kerby2000/NorthPoleCircuit/PCB/Pictures/IMG_1404.jpg

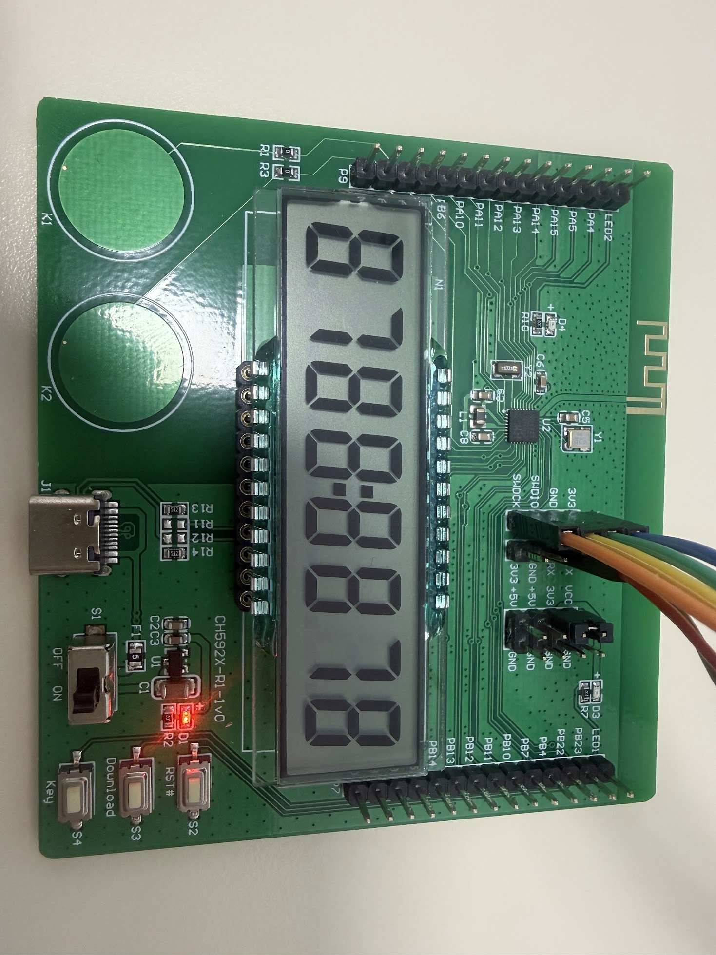
PCB/Pictures/IMG_1404.jpg
