kerby2000/NorthPoleCircuit/PCB/Pictures/IMG_1406.jpg

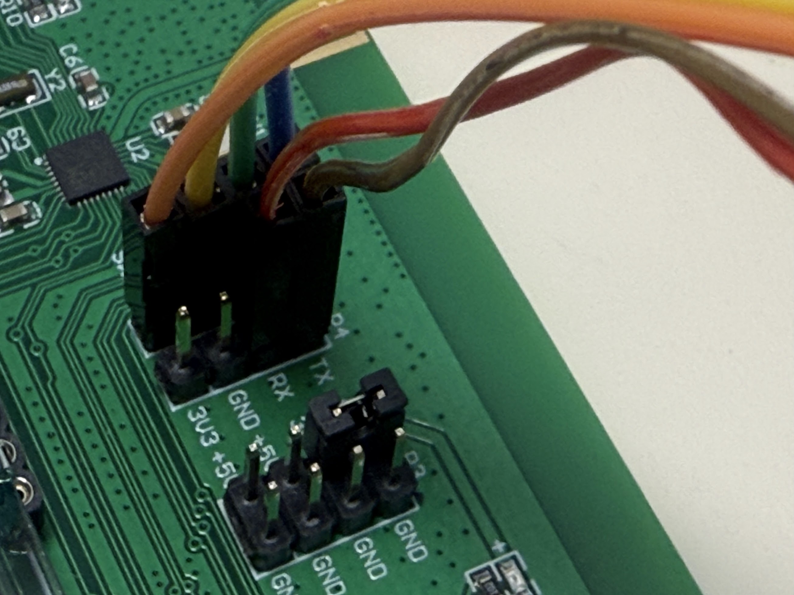
PCB/Pictures/IMG_1406.jpg
