kerby2000/NorthPoleCircuit/PCB/Pictures/IMG_1407.jpg

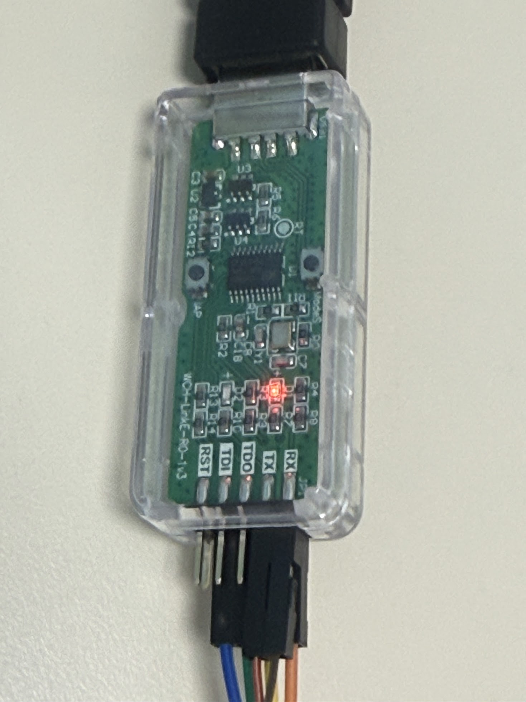
PCB/Pictures/IMG_1407.jpg
