kerby2000/NorthPoleCircuit/PCB/Pictures/IMG_1408.jpg

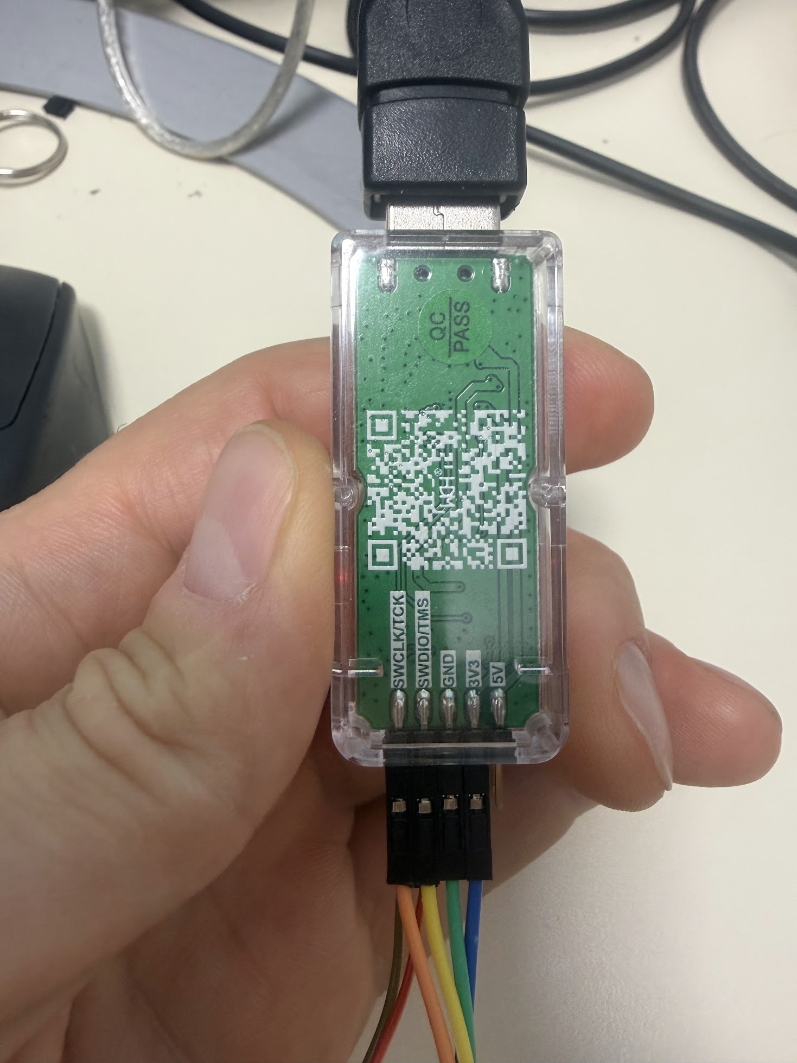
PCB/Pictures/IMG_1408.jpg
