kerby2000/NorthPoleCircuit/Firmware/docs/upload_logs/official_wchisp_tool_result.md

# Official WCH USB ISP Tool Result

Status: PASS, GUI path only

Purpose:

Test the same known-good MounRiver LED probe HEX with the official WCH USB ISP tool.

Input:

```text
Firmware/mounriver_ch592_led_probe/obj/mounriver_ch592_led_probe.hex
```

Record:

- Official tool name/version: WCHISPStudio V3.9, internal `WCHISPTool_CH57x-59x` V3.10.
- Driver binding for `4348:55E0`: official WCH CH375/WCHLink driver stack, not WinUSB/libusb.
- Chip series/model: CH59x / CH592.
- Download port: USB.
- Download config pin: PB22.
- Target file: HEX generated by the probe build, including `Firmware/platformio_ch592_probe/.pio/build/ch592x_wlink_download_mode/firmware.hex` and the known-good MounRiver LED probe HEX candidates.
- Erase/program/verify: PASS.
- Application runs after reset: PASS for LED/LCD-segment probe behavior.

Observed WCHISPStudio V3.9 log:

```text
Device#0 UID:44-46-8F-88-19-70-EC-3E, BTVER:02.30
Begin to download...
BTVER:02.30
Erasing...
Erasing Len: 8K
complete
Programing...
complete
Verifying...
complete
Succeed!
time used:0.358s
```

Interpretation:

```text
Official WCHISPStudio proves that the CH592 native USB Download path, PB22 Download sequence,
USB cable, target power, and HEX image are valid.

The failure of ch32-rs/wchisp is not evidence that native USB ISP is electrically broken.
It is a tool/driver binding problem on Windows.
```

## Protection/Unprotect Finding

WCHISPStudio V3.9 can still flash a CH592 through native USB Download mode after the chip is put in
a protected state, but the tested GUI did not provide an obvious way to unprotect/restore WCH-LinkE
debug attach.

Observed protected-state symptoms:

```text
WCH-LinkUtility / MounRiver:
chip type is not matched or status of chip is wrong

wlink:
Probe is not attached to an MCU, or debug is not enabled
```

Working recovery:

```powershell
# Put CH592 into Download mode.
# Temporarily bind 4348:55E0 / USB Module to WinUSB with Zadig.
$wchisp = "$env:USERPROFILE\.platformio\packages\tool-wchisp\wchisp.exe"
& $wchisp config unprotect
```

After this command, WCH-LinkUtility and MounRiver identified the chip again.

Bring-up rule: keep `Code and data protection mode` unchecked in WCHISPStudio unless intentionally
locking a final production device.

## Command-Line Gap

WCH's WCHISPTool_CMD package was downloaded and inspected.

Observed package contents:

```text
Linux: binaries, source, ISP library/header files
macOS: binary archive and library
Windows: README.md only
```

The Windows README points to the WCHISPTool setup download page. Installing WCHISPTool_Setup.exe
provided WCHISPStudio GUI tools, but no `WCHISPTool_CMD.exe` was found in the tested installation.

Until a Windows WCH-driver-based command-line executable is found or built, the production-safe USB
ISP path is GUI-only.
