kerby2000/NorthPoleCircuit/Firmware/northpole_ch592_bringup/APP/include/board_pins.h

#ifndef BOARD_PINS_H
#define BOARD_PINS_H

#include "board.h"
#include "board_pins_autogen_notes.h"

extern const board_pin_t BOARD_PIN_PWM_A1;
extern const board_pin_t BOARD_PIN_PWM_A2;
extern const board_pin_t BOARD_PIN_PWM_B1;
extern const board_pin_t BOARD_PIN_PWM_B2;
extern const board_pin_t BOARD_PIN_PWM_G1;
extern const board_pin_t BOARD_PIN_PWM_G2;
extern const board_pin_t BOARD_PIN_RGB_DATA;
extern const board_pin_t BOARD_PIN_MOTOR_SLEEP;
extern const board_pin_t BOARD_PIN_AUDIO_BUSY;
extern const board_pin_t BOARD_PIN_HALL1;
extern const board_pin_t BOARD_PIN_HALL2;
extern const board_pin_t BOARD_PIN_TOUCH_SPD_MINUS;
extern const board_pin_t BOARD_PIN_TOUCH_RUN;
extern const board_pin_t BOARD_PIN_TOUCH_SPD_PLUS;
extern const board_pin_t BOARD_PIN_TOUCH_MUSIC;
extern const board_pin_t BOARD_PIN_IP5209_INT;
extern const board_pin_t BOARD_PIN_I2C_SCL;
extern const board_pin_t BOARD_PIN_I2C_SDA;
extern const board_pin_t BOARD_PIN_UART1_TX;
extern const board_pin_t BOARD_PIN_UART1_RX;
extern const board_pin_t BOARD_PIN_USB_DP;
extern const board_pin_t BOARD_PIN_USB_DN;
extern const board_pin_t BOARD_PIN_ANTENNA;

#endif /* BOARD_PINS_H */
