kerby2000/NorthPoleCircuit/Firmware/tools/scope/ip5209_lx_capture.py

#!/usr/bin/env python3
"""Capture IP5209 CSIN/LX waveforms with an OWON/HANMATEK DOS1104 scope."""

from __future__ import annotations

import argparse
import csv
from dataclasses import dataclass, field
from datetime import datetime, timezone
import json
import math
import statistics
import time
from pathlib import Path
import sys
from typing import Any

if __package__ is None or __package__ == "":
    sys.path.insert(0, str(Path(__file__).resolve().parent))

from scope_driver_adapter import ChannelConfig, OwonScopeAdapter, ScopeConnection


REPO_ROOT = Path(__file__).resolve().parents[3]
DEFAULT_EVIDENCE_DIR = REPO_ROOT / "Firmware" / "docs" / "ip5209_scope_evidence"
DEFAULT_REPORT_PATH = REPO_ROOT / "Firmware" / "docs" / "ip5209_lx_scope_report.md"
DEFAULT_FIRMWARE_IMAGE = "Firmware/build/bringup/northpole_ch592_bringup.hex"


@dataclass
class PulseCandidate:
    channel: int
    start_s: float
    end_s: float
    width_s: float
    baseline_v: float
    min_v: float
    max_v: float
    amplitude_v: float
    direction: str
    sample_count: int


@dataclass
class WaveformStats:
    channel: int
    signal: str
    sample_count: int
    min_v: float
    max_v: float
    mean_v: float
    peak_to_peak_v: float
    edge_count: int = 0
    estimated_frequency_hz: float | None = None
    pulse_count: int = 0
    first_pulse_s: float | None = None
    largest_pulse_v: float | None = None
    largest_pulse_width_s: float | None = None


@dataclass
class ScaleCheck:
    channel: int
    signal: str
    dmm_reference_v: float
    raw_mean_v: float
    ratio: float
    status: str


@dataclass
class CaptureResult:
    label: str
    mode: str
    screenshot_path: Path | None = None
    csv_path: Path | None = None
    trigger_status: str | None = None
    classification: str = "PENDING_CAPTURE"
    stats: list[WaveformStats] = field(default_factory=list)
    pulses: dict[int, list[PulseCandidate]] = field(default_factory=dict)
    scale_checks: list[ScaleCheck] = field(default_factory=list)
    scope_settings: dict[str, Any] = field(default_factory=dict)
    warnings: list[str] = field(default_factory=list)
    notes: list[str] = field(default_factory=list)


def build_parser() -> argparse.ArgumentParser:
    parser = argparse.ArgumentParser(description=__doc__)
    parser.add_argument(
        "--mode",
        choices=["idle", "wake-single", "steady-switching", "load-test"],
        help="Capture mode.",
    )
    parser.add_argument("--check-scope", action="store_true", help="Only open the scope and query *IDN?.")
    parser.add_argument(
        "--rewrite-report-only",
        action="store_true",
        help="Reanalyze existing capture CSV files from the manifest and rebuild the report without opening the scope.",
    )
    parser.add_argument("--out-dir", default=str(DEFAULT_EVIDENCE_DIR), help="Evidence output directory.")
    parser.add_argument("--report", default=str(DEFAULT_REPORT_PATH), help="Markdown report path.")
    parser.add_argument(
        "--instrumentkit-src",
        default=str(Path.home() / "Documents" / "VS code projects" / "InstrumentKit" / "src"),
        help="Path to local InstrumentKit src.",
    )
    parser.add_argument("--vid", default="0x5345", help="Scope USB VID.")
    parser.add_argument("--pid", default="0x1234", help="Scope USB PID.")
    parser.add_argument("--timeout-s", type=float, default=2.0, help="Scope USB timeout.")
    parser.add_argument("--probe", type=int, default=1, help="Probe attenuation configured on the scope.")
    parser.add_argument("--ch1-scale", type=float, default=2.0, help="CH1 volts/div.")
    parser.add_argument("--ch2-scale", type=float, default=2.0, help="CH2 volts/div.")
    parser.add_argument("--ch3", choices=["off", "vout"], default="off", help="Optional CH3 signal.")
    parser.add_argument("--ch4", choices=["off", "key", "vreg"], default="off", help="Optional CH4 signal.")
    parser.add_argument("--ch3-scale", type=float, default=2.0, help="CH3 volts/div.")
    parser.add_argument("--ch4-scale", type=float, default=1.0, help="CH4 volts/div.")
    parser.add_argument("--ch1-dmm-v", type=float, default=None, help="Optional DMM reference voltage for CH1.")
    parser.add_argument("--ch2-dmm-v", type=float, default=None, help="Optional DMM reference voltage for CH2.")
    parser.add_argument("--ch3-dmm-v", type=float, default=None, help="Optional DMM reference voltage for CH3.")
    parser.add_argument("--ch4-dmm-v", type=float, default=None, help="Optional DMM reference voltage for CH4.")
    parser.add_argument(
        "--pulse-min-vpp",
        type=float,
        default=0.5,
        help="Minimum peak-to-peak voltage before a channel can be treated as pulsing.",
    )
    parser.add_argument(
        "--pulse-threshold-v",
        type=float,
        default=0.5,
        help="Minimum excursion from baseline for pulse candidate detection.",
    )
    parser.add_argument("--idle-timebase", type=float, default=0.010, help="Idle seconds/div.")
    parser.add_argument("--wake-timebase", type=float, default=0.000100, help="Wake seconds/div.")
    parser.add_argument("--trigger-level", type=float, default=2.0, help="CH2 falling-edge trigger level.")
    parser.add_argument("--wait-trigger-s", type=float, default=10.0, help="Wake trigger wait time.")
    parser.add_argument("--no-waveform", action="store_true", help="Skip waveform CSV reads.")
    parser.add_argument("--no-screenshot", action="store_true", help="Skip screenshot capture.")
    parser.add_argument("--no-prompt", action="store_true", help="Do not wait for user prompts.")
    parser.add_argument("--board-revision", default="north-pole-ble-audio-current-pcb")
    parser.add_argument("--firmware-image", default=DEFAULT_FIRMWARE_IMAGE)
    parser.add_argument("--battery-voltage", default="unknown")
    parser.add_argument("--usb-state", default="unknown", help="connected, disconnected, or unknown.")
    parser.add_argument("--load-ohms", default="220", help="Load value for load-test report text.")
    return parser


def main(argv: list[str] | None = None) -> int:
    parser = build_parser()
    args = parser.parse_args(argv)
    if not args.check_scope and not args.rewrite_report_only and args.mode is None:
        parser.error("--mode is required unless --check-scope is used")

    out_dir = Path(args.out_dir)
    out_dir.mkdir(parents=True, exist_ok=True)

    if args.rewrite_report_only:
        records = load_manifest(out_dir)
        records = reanalyze_records(records, args)
        write_manifest(out_dir, records)
        write_report(Path(args.report), records)
        print(f"report={Path(args.report)}")
        return 0

    connection = ScopeConnection(
        instrumentkit_src=Path(args.instrumentkit_src),
        vid=int(str(args.vid), 0),
        pid=int(str(args.pid), 0),
        timeout_s=args.timeout_s,
    )

    with OwonScopeAdapter(connection) as scope:
        scope_idn = scope.identify()
        if args.check_scope:
            print(f"scope_idn={scope_idn}")
            return 0

        if args.mode == "idle":
            results = [capture_idle(scope, args, out_dir)]
        elif args.mode == "wake-single":
            results = [capture_wake_single(scope, args, out_dir, label_suffix="wake_single")]
        elif args.mode == "load-test":
            results = [capture_load_test(scope, args, out_dir)]
        else:
            results = capture_steady_switching(scope, args, out_dir)

    records = update_manifest(out_dir, args, scope_idn, results)
    write_report(Path(args.report), records)
    for result in results:
        print(f"{result.label}: classification={result.classification}")
        if result.screenshot_path:
            print(f"  screenshot={result.screenshot_path}")
        if result.csv_path:
            print(f"  csv={result.csv_path}")
    return 0


def capture_idle(scope: OwonScopeAdapter, args: argparse.Namespace, out_dir: Path) -> CaptureResult:
    label = timestamped_label("idle")
    configure_channels(scope, args)
    scope.set_timebase_scale(args.idle_timebase)
    scope.run()
    time.sleep(0.5)
    scope.stop()
    return finish_capture(scope, args, out_dir, label, mode="idle")


def capture_wake_single(
    scope: OwonScopeAdapter,
    args: argparse.Namespace,
    out_dir: Path,
    *,
    label_suffix: str,
) -> CaptureResult:
    label = timestamped_label(label_suffix)
    configure_channels(scope, args)
    scope.set_timebase_scale(args.wake_timebase)
    scope.configure_edge_trigger(
        source_channel=2,
        slope="falling",
        level_v=args.trigger_level,
        sweep="SINGle",
    )
    scope.single()
    if not args.no_prompt:
        input("Scope is armed. Press SW3 briefly, wait for the trigger, then press Enter here.")
    status = wait_for_trigger(scope, args.wait_trigger_s)

    result = finish_capture(scope, args, out_dir, label, mode="wake-single", trigger_status=status)
    if result.classification == "NO_LX_SWITCHING_DETECTED":
        result.notes.append(
            "Falling-edge trigger did not show LX activity. Try a rising-edge capture at 4.5 V if needed."
        )
    return result


def capture_load_test(scope: OwonScopeAdapter, args: argparse.Namespace, out_dir: Path) -> CaptureResult:
    if not args.no_prompt:
        input(f"Confirm {args.load_ohms} ohm load is connected from +5V to GND, then press Enter.")
    return capture_wake_single(scope, args, out_dir, label_suffix=f"load_{args.load_ohms}R_wake_single")


def capture_steady_switching(
    scope: OwonScopeAdapter,
    args: argparse.Namespace,
    out_dir: Path,
) -> list[CaptureResult]:
    if not args.no_prompt:
        input("Press SW3 and confirm VREG is awake if possible, then press Enter for steady captures.")

    results: list[CaptureResult] = []
    for timebase in (500e-9, 1e-6, 2e-6, 5e-6):
        label = timestamped_label(f"steady_{format_timebase(timebase)}div")
        configure_channels(scope, args)
        scope.set_timebase_scale(timebase)
        scope.configure_edge_trigger(
            source_channel=2,
            slope="falling",
            level_v=args.trigger_level,
            sweep="NORMal",
        )
        scope.run()
        time.sleep(0.5)
        scope.stop()
        results.append(finish_capture(scope, args, out_dir, label, mode="steady-switching"))
    return results


def configure_channels(scope: OwonScopeAdapter, args: argparse.Namespace) -> None:
    configs = [
        ChannelConfig(1, True, args.ch1_scale, probe_attenuation=args.probe),
        ChannelConfig(2, True, args.ch2_scale, probe_attenuation=args.probe),
        ChannelConfig(3, args.ch3 != "off", args.ch3_scale, probe_attenuation=args.probe),
        ChannelConfig(4, args.ch4 != "off", args.ch4_scale, probe_attenuation=args.probe),
    ]
    for config in configs:
        scope.setup_channel(config)


def wait_for_trigger(scope: OwonScopeAdapter, timeout_s: float) -> str | None:
    deadline = time.monotonic() + max(timeout_s, 0.0)
    last_status: str | None = None
    while time.monotonic() < deadline:
        last_status = scope.trigger_status()
        if last_status and any(token in last_status.upper() for token in ("STOP", "TRIG", "TD")):
            return last_status
        time.sleep(0.2)
    return last_status


def finish_capture(
    scope: OwonScopeAdapter,
    args: argparse.Namespace,
    out_dir: Path,
    label: str,
    *,
    mode: str,
    trigger_status: str | None = None,
) -> CaptureResult:
    screenshot_path: Path | None = None
    if not args.no_screenshot:
        screenshot_path = scope.save_screenshot(out_dir / f"{label}.png")

    waveforms: dict[int, tuple[list[float], list[float]]] = {}
    if not args.no_waveform:
        for channel in enabled_channels(args):
            waveform = scope.read_waveform(channel)
            if waveform is not None:
                waveforms[channel] = waveform

    csv_path: Path | None = None
    if waveforms:
        csv_path = out_dir / f"{label}_{channel_suffix(sorted(waveforms))}.csv"
        scope.save_waveforms_csv(csv_path, waveforms)

    stats, pulses = analyze_waveforms(waveforms, args)
    scale_checks, scale_warnings = build_scale_checks(stats, args)
    classification = classify_capture(stats, pulses, scale_warnings)
    scope_settings = scope.read_scope_settings(enabled_channels(args))
    return CaptureResult(
        label=label,
        mode=mode,
        screenshot_path=screenshot_path,
        csv_path=csv_path,
        trigger_status=trigger_status,
        classification=classification,
        stats=stats,
        pulses=pulses,
        scale_checks=scale_checks,
        scope_settings=scope_settings,
        warnings=scale_warnings,
    )


def enabled_channels(args: argparse.Namespace) -> list[int]:
    channels = [1, 2]
    if args.ch3 != "off":
        channels.append(3)
    if args.ch4 != "off":
        channels.append(4)
    return channels


def channel_suffix(channels: list[int]) -> str:
    return "_".join(f"ch{channel}" for channel in channels)


def channel_signal(channel: int, args_or_record: argparse.Namespace | dict[str, Any] | None = None) -> str:
    if channel == 1:
        return "CSIN"
    if channel == 2:
        return "LX"
    if channel == 3:
        if isinstance(args_or_record, argparse.Namespace) and getattr(args_or_record, "ch3", "off") == "vout":
            return "VOUT"
        return "VOUT"
    if channel == 4:
        if isinstance(args_or_record, argparse.Namespace):
            value = getattr(args_or_record, "ch4", "off")
            if value == "key":
                return "KEY"
            if value == "vreg":
                return "VREG"
        return "VREG/KEY"
    return f"CH{channel}"


def analyze_waveforms(
    waveforms: dict[int, tuple[list[float], list[float]]],
    args: argparse.Namespace,
) -> tuple[list[WaveformStats], dict[int, list[PulseCandidate]]]:
    stats: list[WaveformStats] = []
    pulses: dict[int, list[PulseCandidate]] = {}
    for channel in sorted(waveforms):
        channel_stats, channel_pulses = analyze_channel(
            channel,
            *waveforms[channel],
            signal=channel_signal(channel, args),
            pulse_min_vpp=args.pulse_min_vpp,
            pulse_threshold_v=args.pulse_threshold_v,
        )
        stats.append(channel_stats)
        pulses[channel] = channel_pulses
    return stats, pulses


def analyze_channel(
    channel: int,
    times: list[float],
    volts: list[float],
    *,
    signal: str = "",
    pulse_min_vpp: float = 0.5,
    pulse_threshold_v: float = 0.5,
) -> tuple[WaveformStats, list[PulseCandidate]]:
    count = min(len(times), len(volts))
    values = volts[:count]
    if count == 0:
        return (
            WaveformStats(channel, signal or f"CH{channel}", 0, math.nan, math.nan, math.nan, math.nan),
            [],
        )
    min_v = min(values)
    max_v = max(values)
    peak_to_peak_v = max_v - min_v
    edge_count = 0
    frequency_hz: float | None = None
    pulses: list[PulseCandidate] = []
    if peak_to_peak_v >= pulse_min_vpp:
        edge_count, frequency_hz = estimate_edges_and_frequency(
            times[:count],
            values,
            min_vpp=pulse_min_vpp,
        )
        pulses = find_pulse_candidates(
            channel,
            times[:count],
            values,
            threshold_v=pulse_threshold_v,
            min_vpp=pulse_min_vpp,
        )
    return (
        WaveformStats(
            channel=channel,
            signal=signal or f"CH{channel}",
            sample_count=count,
            min_v=min_v,
            max_v=max_v,
            mean_v=statistics.fmean(values),
            peak_to_peak_v=peak_to_peak_v,
            edge_count=edge_count,
            estimated_frequency_hz=frequency_hz,
            pulse_count=len(pulses),
            first_pulse_s=pulses[0].start_s if pulses else None,
            largest_pulse_v=max((pulse.amplitude_v for pulse in pulses), default=None),
            largest_pulse_width_s=max((pulse.width_s for pulse in pulses), default=None),
        ),
        pulses,
    )
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
